lemmi25/NixiTubeClock/src/nixiDriver.cpp

#include <nixiDriver.h>
#include <Shifty.h>

// nixiDriver translates logical digits into shift-register bit patterns for
// either 4-bit Nixie encoding or 8-bit Numitron segment encoding.

nixiDriver::nixiDriver(uint8_t DS, uint8_t SH, uint8_t ST, bool numitron)
{
    this->numitron = numitron;

    if (this->numitron == true)
    {
        this->nixiShift.setBitCount(32);
    }
    else
    {
        // clock has 2 shift registers for nixie mode
        this->nixiShift.setBitCount(16);
    }

    this->nixiShift.setPins(DS, SH, ST);
}

uint8_t nixiDriver::writeSegment(uint8_t number, uint8_t segment)
{
    if (this->numitron == false)
    {
        // Nixie mode: each tube uses a 4-bit BCD-like pattern.
        bool truthTableNumber[4];
        nixiDriver::writeNumber(number, truthTableNumber);
        switch (segment)
        {
        case 1:
            this->nixiShift.writeBit(4, truthTableNumber[0]);
            this->nixiShift.writeBit(5, truthTableNumber[1]);
            this->nixiShift.writeBit(6, truthTableNumber[2]);
            this->nixiShift.writeBit(7, truthTableNumber[3]);
            break;
        case 2:
            this->nixiShift.writeBit(0, truthTableNumber[0]);
            this->nixiShift.writeBit(1, truthTableNumber[1]);
            this->nixiShift.writeBit(2, truthTableNumber[2]);
            this->nixiShift.writeBit(3, truthTableNumber[3]);
            break;
        case 3:
            this->nixiShift.writeBit(8, truthTableNumber[0]);
            this->nixiShift.writeBit(9, truthTableNumber[1]);
            this->nixiShift.writeBit(10, truthTableNumber[2]);
            this->nixiShift.writeBit(11, truthTableNumber[3]);
            break;
        case 4:
            this->nixiShift.writeBit(12, truthTableNumber[0]);
            this->nixiShift.writeBit(13, truthTableNumber[1]);
            this->nixiShift.writeBit(14, truthTableNumber[2]);
            this->nixiShift.writeBit(15, truthTableNumber[3]);
            break;

        default:
            return 0;
            break;
        }
    }
    else
    {
        // Numitron mode: each tube uses 8 segment control bits.
        bool truthTableNumber[8];
        nixiDriver::writeNumber(number, truthTableNumber);
        switch (segment)
        {
        case 1:
            this->nixiShift.writeBit(0, truthTableNumber[0]);
            this->nixiShift.writeBit(1, truthTableNumber[1]);
            this->nixiShift.writeBit(2, truthTableNumber[2]);
            this->nixiShift.writeBit(3, truthTableNumber[3]);
            this->nixiShift.writeBit(4, truthTableNumber[4]);
            this->nixiShift.writeBit(5, truthTableNumber[5]);
            this->nixiShift.writeBit(6, truthTableNumber[6]);
            this->nixiShift.writeBit(7, truthTableNumber[7]);
            break;
        case 2:
            this->nixiShift.writeBit(8, truthTableNumber[0]);
            this->nixiShift.writeBit(9, truthTableNumber[1]);
            this->nixiShift.writeBit(10, truthTableNumber[2]);
            this->nixiShift.writeBit(11, truthTableNumber[3]);
            this->nixiShift.writeBit(12, truthTableNumber[4]);
            this->nixiShift.writeBit(13, truthTableNumber[5]);
            this->nixiShift.writeBit(14, truthTableNumber[6]);
            this->nixiShift.writeBit(15, truthTableNumber[7]);
            break;
        case 3:
            this->nixiShift.writeBit(16, truthTableNumber[0]);
            this->nixiShift.writeBit(17, truthTableNumber[1]);
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
    nixiDriver::writeSegment(10, 4);

    delay(1000);
}

void nixiDriver::off()
{
    // Digit 10 is used as "blank" in both mappings.
    nixiDriver::writeSegment(10, 1);
    nixiDriver::writeSegment(10, 2);
    nixiDriver::writeSegment(10, 3);
    nixiDriver::writeSegment(10, 4);
}
