lemmi25/NixiTubeClock/src/main.cpp

/* Code written by Moritz Boesenberg 26/12/2019 under the MIT licence
 *
 * NOTE: This file is intentionally minimal and is NOT compiled by the
 * active PlatformIO hardware profiles.
 *
 * Active firmware entry points:
 * - src/hardware/master_no_rtc.cpp
 * - src/hardware/rtc_local.cpp
 */

#include <Arduino.h>

void setup()
{
	// Intentionally empty: active firmware profiles define their own setup().
}

void loop()
{
	// Intentionally empty: active firmware profiles define their own loop().
}
